lukasz-tuz/rgb-butterfly/docs/monarch-butterfly-panel.png

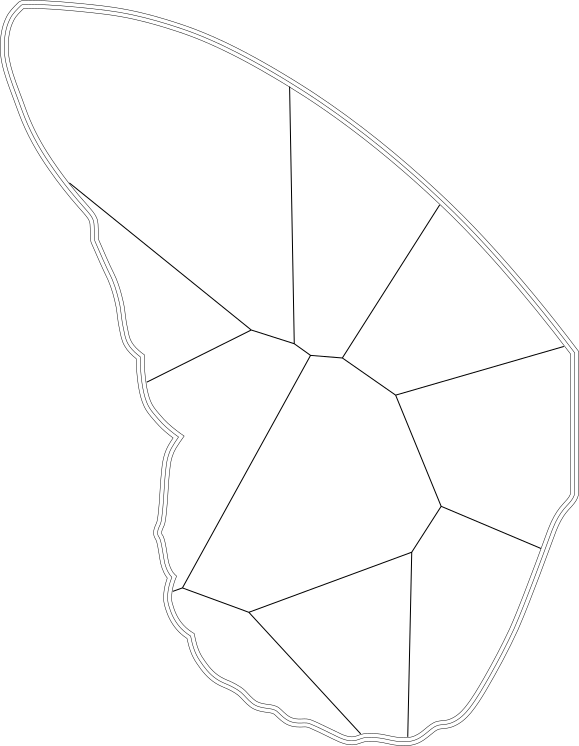
docs/monarch-butterfly-panel.png
