lukasz-tuz/rgb-butterfly/docs/P3141081.JPG

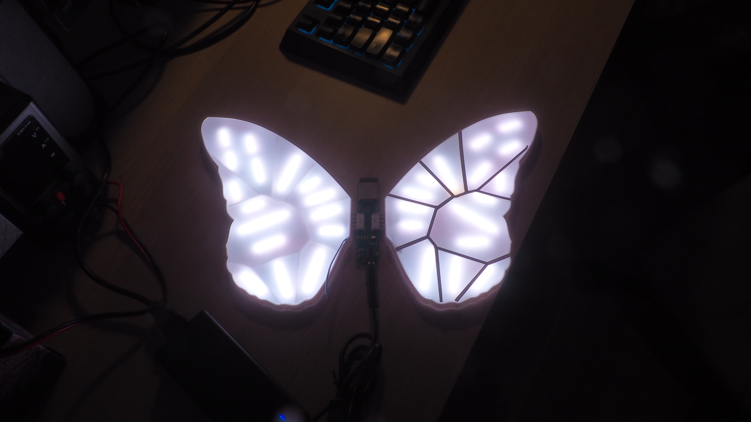
docs/P3141081.JPG
